visakhanc/usb-ir/firmware/hid-ir-remote/ir_config.h

/*
 * 	This file containts configuration defintion for Infrared(IR) receiver library for AVR 
 *
 */


/* Defines the external interrupt used to connect ouput pin of IR receiver - Define this to INT0 or INT1 */
#define IR_INTERRUPT	INT1
